wardru/Klotz/Firmware/buz.h

#ifndef BUZ_H
 #define BUZ_H

 #define BUZ_SPEAKER_X  30
 #define BUZ_SPEAKER_Y  33

 #define BUZ_CROSS_X    BUZ_SPEAKER_X + 49
 #define BUZ_CROSS_Y    BUZ_SPEAKER_Y + 21

 #define BUZ_WAVES_X    BUZ_SPEAKER_X + 49
 #define BUZ_WAVES_Y    BUZ_SPEAKER_Y + 14

 extern const unsigned char waves_G[1360];
 extern const unsigned char cross_R[800];
 extern const unsigned char speaker[5454];

#endif
